BoujeeEnjinia1701/noisemap/cad/drawings/NSM-DWG-101.pdf

### BUILD PLAN SKETCH, PLAN NOT YET BUILT NoiseMap · github.com/BoujeeEnjinia1701/noisemap

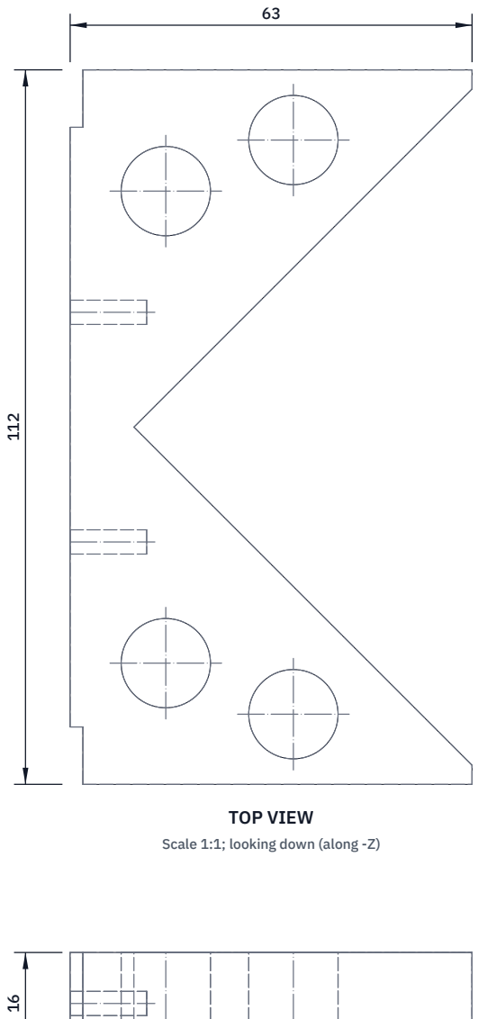
[picture p35: figure]
TOP VIEW; Scale 1:1; looking down (along -Z)

FRONT VIEW
Scale 1:1; looking at the front (along +Y)

RIGHT VIEW
Scale 1:1; looking at the right side (along -X)

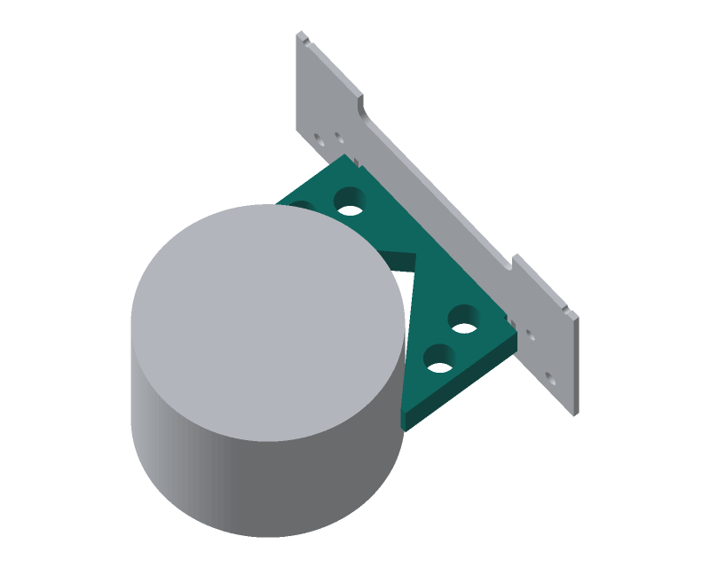
[picture p36: figure]

WHERE IT GOES
This part in colour, its neighbours in grey

HOW TO MAKE IT AND HOW IT FITS
Make two. Saw 112 mm off 70 x 16 mm bar; saw and file the width to 63 mm. The 112 x 16 face is the back; file it flat.
Scribe a 90 degree V on both 112 x 63 faces with a 45 degree square: 106 mm wide at the front face, point 10 mm from the back face.
Saw just inside both lines, file to the lines; keep the faces flat.
Rebate each back corner 9 mm wide and 2 mm deep, full height: the band passes under it. Round the front outer corners 3 mm. Drill four 14 mm lightening holes through: 15 mm from the back at 37 mm each side, and 35 mm from the back at 45 mm each side. Drill 3.3 mm, 14 deep, tap M4 12 deep in the back face at 18 mm each side of centre, half way up (8 mm).
Fit: two M4 countersunk screws from the box side of the FieldNode back plate. A 114 mm pole touches both V faces 40 mm off centre. Check: on a 114 mm tube the block must not rock.
REV | DESCRIPTION | DATE | BY
P1 | Making sketch for the prototype build plan | 2026-10-01 | AC
NOISEMAP | github.com/BoujeeEnjinia1701/noisemap

## NoiseMap street pole V-block (make 2): making sketch

DRAWING NO.
NSM-DWG-101

REV
P1

SHEET
1 of 1

SIZE

## ANSI B

SCALE
1:1

UNITS
mm
PROJECTION | DATE
2026-10-01

DRAWN
Amish Chadha

MATERIAL / NOTES
Aluminium flat bar 70 x 16 mm, 6082 or 6061 class
Licensed CERN-OHL-S-2.0 · Design Molecule Lab · designmolecule.com | Generated from cad/src; do not edit by hand
