BoujeeEnjinia1701/noisemap/cad/drawings/NSM-DWG-102.pdf

### BUILD PLAN SKETCH, PLAN NOT YET BUILT NoiseMap · github.com/BoujeeEnjinia1701/noisemap

FRONT VIEW
Scale 1:2; looking at the front (along +Y)

TOP VIEW
Scale 1:2; looking down (along -Z)

RIGHT VIEW
Scale 1:2; looking at the right side (along -X)

65

114 124

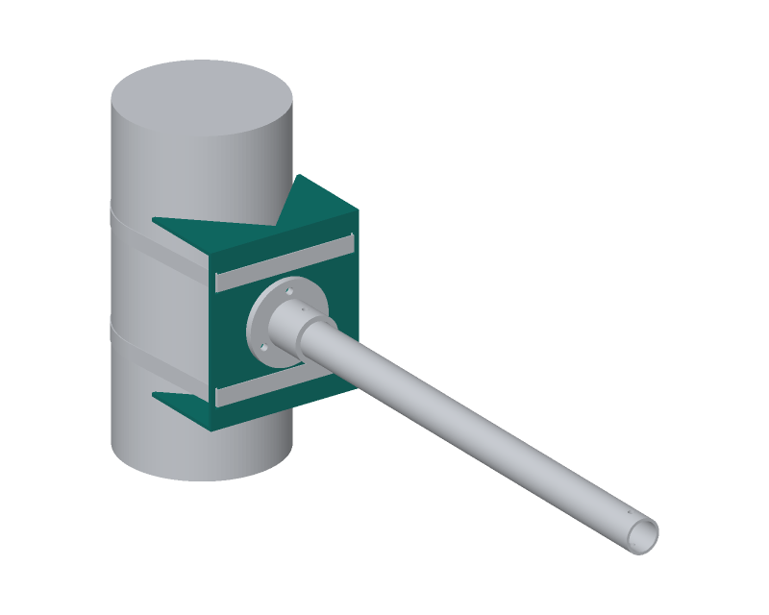
[picture p37: figure]

WHERE IT GOES
This part in colour, its neighbours in grey

HOW TO MAKE IT AND HOW IT FITS
A channel: web 114 wide x 124 tall, two flanges standing 65 out (outside sizes). Blank 114 wide; the bending shop sets its length. Cut a 90 degree V in each end of the blank (these become the flanges): 109 mm wide at the end, point 54.5 mm in from the end. Web: four band slots 3 x 15 at 52 mm each side of centre, centred 40 mm above and below the middle; chain drill 3 mm, file square. Web: three 5.5 mm holes on a 45 mm circle round the middle, one straight up, for the tube flange.
Bend both flanges 90 degrees the same way, inside radius about 3. Deburr and round the V edges so they cannot score the pole.
Fit: the pole bears on the four V edges; each band runs round
the pole, through two slots and across the outside of the web. Check: on a 114 mm tube all four V edges touch and it does not rock.
REV | DESCRIPTION | DATE | BY
P1 | Making sketch for the prototype build plan | 2026-10-01 | AC
NOISEMAP | github.com/BoujeeEnjinia1701/noisemap

## NoiseMap arm saddle: making sketch

DRAWING NO.
NSM-DWG-102

REV
P1

SHEET
1 of 1

SIZE

## ANSI B

SCALE
1:2

UNITS
mm
PROJECTION | DATE
2026-10-01

DRAWN
Amish Chadha

MATERIAL / NOTES
Aluminium sheet 2.5 mm, 5052-H32 (bends without cracking)
Licensed CERN-OHL-S-2.0 · Design Molecule Lab · designmolecule.com | Generated from cad/src; do not edit by hand
