BoujeeEnjinia1701/noisemap/cad/drawings/NSM-DWG-103.pdf

### BUILD PLAN SKETCH, PLAN NOT YET BUILT NoiseMap · github.com/BoujeeEnjinia1701/noisemap

FRONT VIEW
Scale 1:2; looking at the front (along +Y)

TOP VIEW
Scale 1:2; looking down (along -Z)

RIGHT VIEW
Scale 1:2; looking at the right side (along -X)

383

25 25

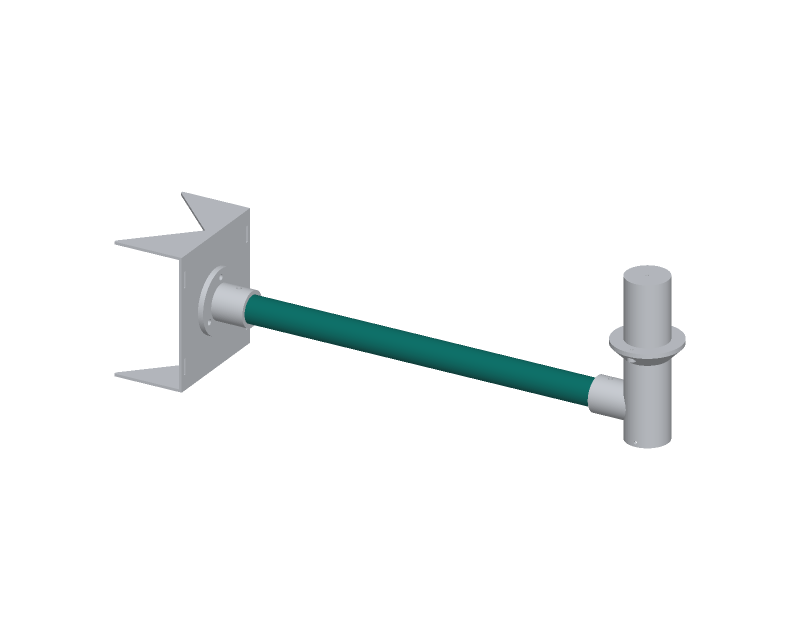
[picture p38: figure]

WHERE IT GOES
This part in colour, its neighbours in grey

HOW TO MAKE IT AND HOW IT FITS
Cut 383 mm of 25 x 2 mm tube; square and deburr both ends. Mark one end as the pole end.
Drill 4.6 mm straight through, top to bottom, 12.5 mm from the pole end (the flange cross bolt).
Drill 4.6 mm straight through, in the same plane, 12.5 mm from the far end (the head cross bolt).
Drill both holes on a drill press with the tube in a V-block so each hole passes through the centre line.
Fit: the pole end goes 25 mm into the tube flange's socket, the far end 25 mm into the head's socket; one bolt through each. Check: both holes line up when you sight along the tube.
REV | DESCRIPTION | DATE | BY
P1 | Making sketch for the prototype build plan | 2026-10-01 | AC
NOISEMAP | github.com/BoujeeEnjinia1701/noisemap

## NoiseMap arm tube: making sketch

DRAWING NO.
NSM-DWG-103

REV
P1

SHEET
1 of 1

SIZE

## ANSI B

SCALE
1:2

UNITS
mm
PROJECTION | DATE
2026-10-01

DRAWN
Amish Chadha

MATERIAL / NOTES
Aluminium round tube 25 x 2 mm, 6063
Licensed CERN-OHL-S-2.0 · Design Molecule Lab · designmolecule.com | Generated from cad/src; do not edit by hand
