BoujeeEnjinia1701/noisemap/cad/drawings/NSM-DWG-104.pdf

### BUILD PLAN SKETCH, PLAN NOT YET BUILT NoiseMap · github.com/BoujeeEnjinia1701/noisemap

FRONT VIEW
Scale 1:2; looking at the front (along +Y)

TOP VIEW
Scale 1:2; looking down (along -Z)

RIGHT VIEW
Scale 1:2; looking at the right side (along -X)

80

64 150

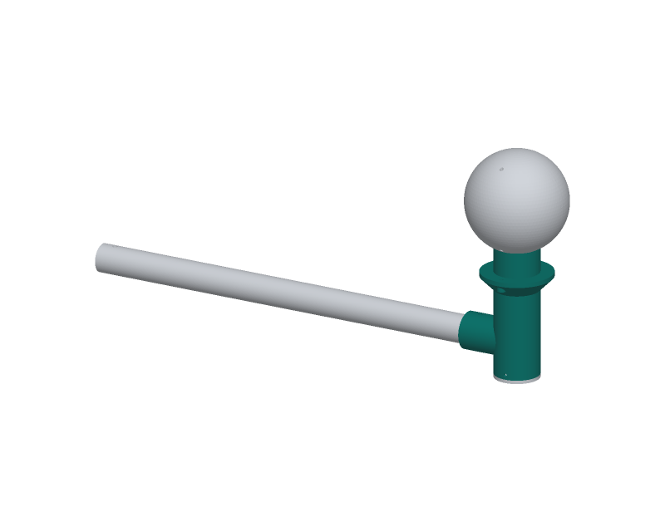
[picture p39: figure]

WHERE IT GOES
This part in colour, its neighbours in grey

HOW TO MAKE IT AND HOW IT FITS
Tube 40 OD x 3 wall x 150 tall, closed at the top by a 2 mm plate with a 3 mm acoustic port on the axis.
Drip skirt 64 OD, its top 58 below the port; 45 degree cone under it so it prints without support. Spike boss on it, 26 off the axis.
Arm socket 33 OD, bore 25.4, 25 deep, its axis 120 below the port; 4.4 mm cross hole 12.5 in from its open end, top to bottom. Inside: two card guides with 1.8 mm slots for the processor board; two 5 mm bosses under the top plate, 20 apart, for the mic board. Two 3.2 mm holes 4 above the open end for the cap screws.
Print standing on the top plate, supports under the arm socket only. Press an M3 heat-set insert into the spike boss.
Check: the port is clear; a 25 mm tube slides into the socket.
REV | DESCRIPTION | DATE | BY
P1 | Making sketch for the prototype build plan | 2026-10-01 | AC
NOISEMAP | github.com/BoujeeEnjinia1701/noisemap

## NoiseMap head housing: making sketch

DRAWING NO.
NSM-DWG-104

REV
P1

SHEET
1 of 1

SIZE

## ANSI B

SCALE
1:2

UNITS
mm
PROJECTION | DATE
2026-10-01

DRAWN
Amish Chadha

MATERIAL / NOTES
ASA, 3D printed, 4 walls, 40 % infill
Licensed CERN-OHL-S-2.0 · Design Molecule Lab · designmolecule.com | Generated from cad/src; do not edit by hand
