BoujeeEnjinia1701/noisemap/cad/drawings/NSM-DWG-105.pdf

### BUILD PLAN SKETCH, PLAN NOT YET BUILT NoiseMap · github.com/BoujeeEnjinia1701/noisemap

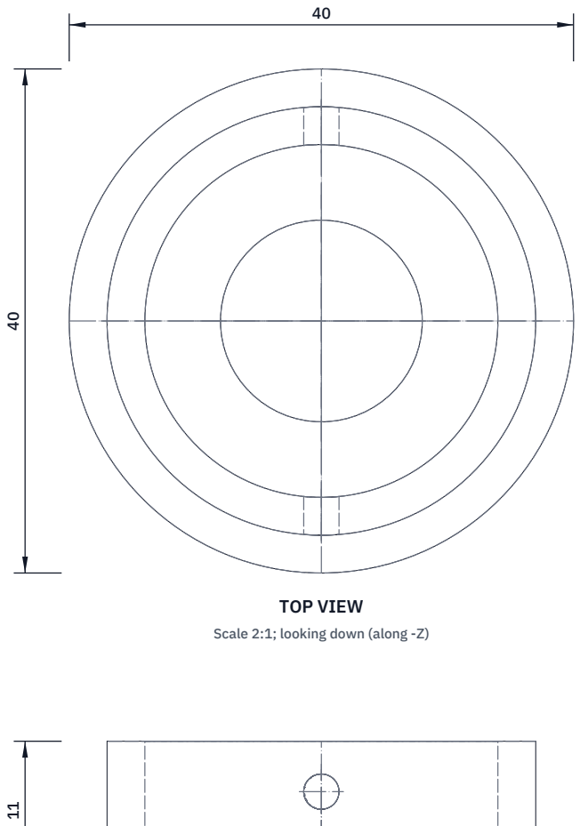
[picture p40: figure]
TOP VIEW; Scale 2:1; looking down (along -Z)

FRONT VIEW
Scale 2:1; looking at the front (along +Y)

RIGHT VIEW
Scale 2:1; looking at the right side (along -X)

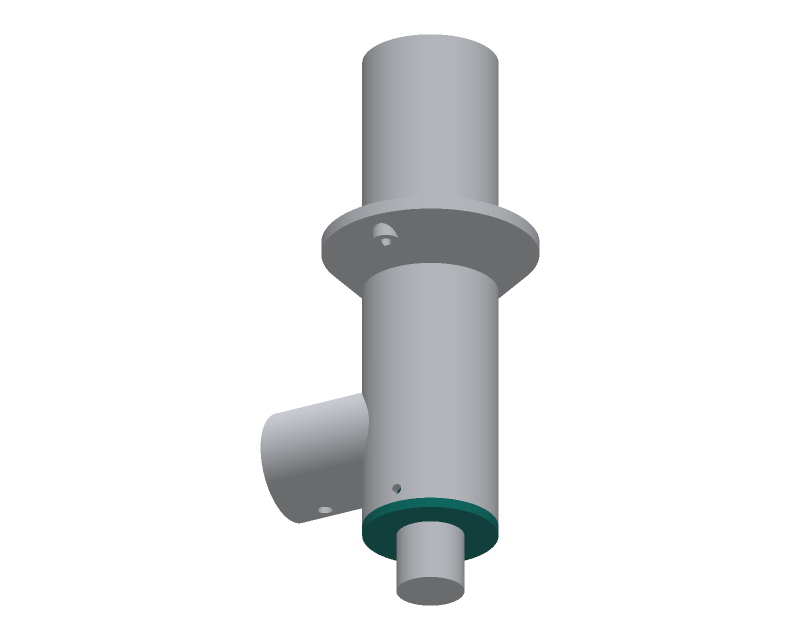
[picture p41: figure]

WHERE IT GOES
This part in colour, its neighbours in grey

HOW TO MAKE IT AND HOW IT FITS
Disc 40 OD x 3 thick with a ring standing 8 on it: 34 OD, 3 wall. 16 mm hole on the axis for the M16 cable gland.
Two 2.8 mm holes across the ring, 4 up from the disc, opposite each other, for the M3 screws (they self-tap into the ring). Print disc down; no supports.
Fit: the ring slides into the open end of the head until the disc meets the tube; two M3 x 6 screws through the head wall.
The gland goes through the 16 mm hole from below, nut inside. Check: the ring slides in by hand; the screw holes line up.
REV | DESCRIPTION | DATE | BY
P1 | Making sketch for the prototype build plan | 2026-10-01 | AC
NOISEMAP | github.com/BoujeeEnjinia1701/noisemap

## NoiseMap head bottom cap: making sketch

DRAWING NO.
NSM-DWG-105

REV
P1

SHEET
1 of 1

SIZE

## ANSI B

SCALE
2:1

UNITS
mm
PROJECTION | DATE
2026-10-01

DRAWN
Amish Chadha

MATERIAL / NOTES
ASA, 3D printed, solid
Licensed CERN-OHL-S-2.0 · Design Molecule Lab · designmolecule.com | Generated from cad/src; do not edit by hand
