BoujeeEnjinia1701/noisemap/cad/drawings/NSM-DWG-001.png

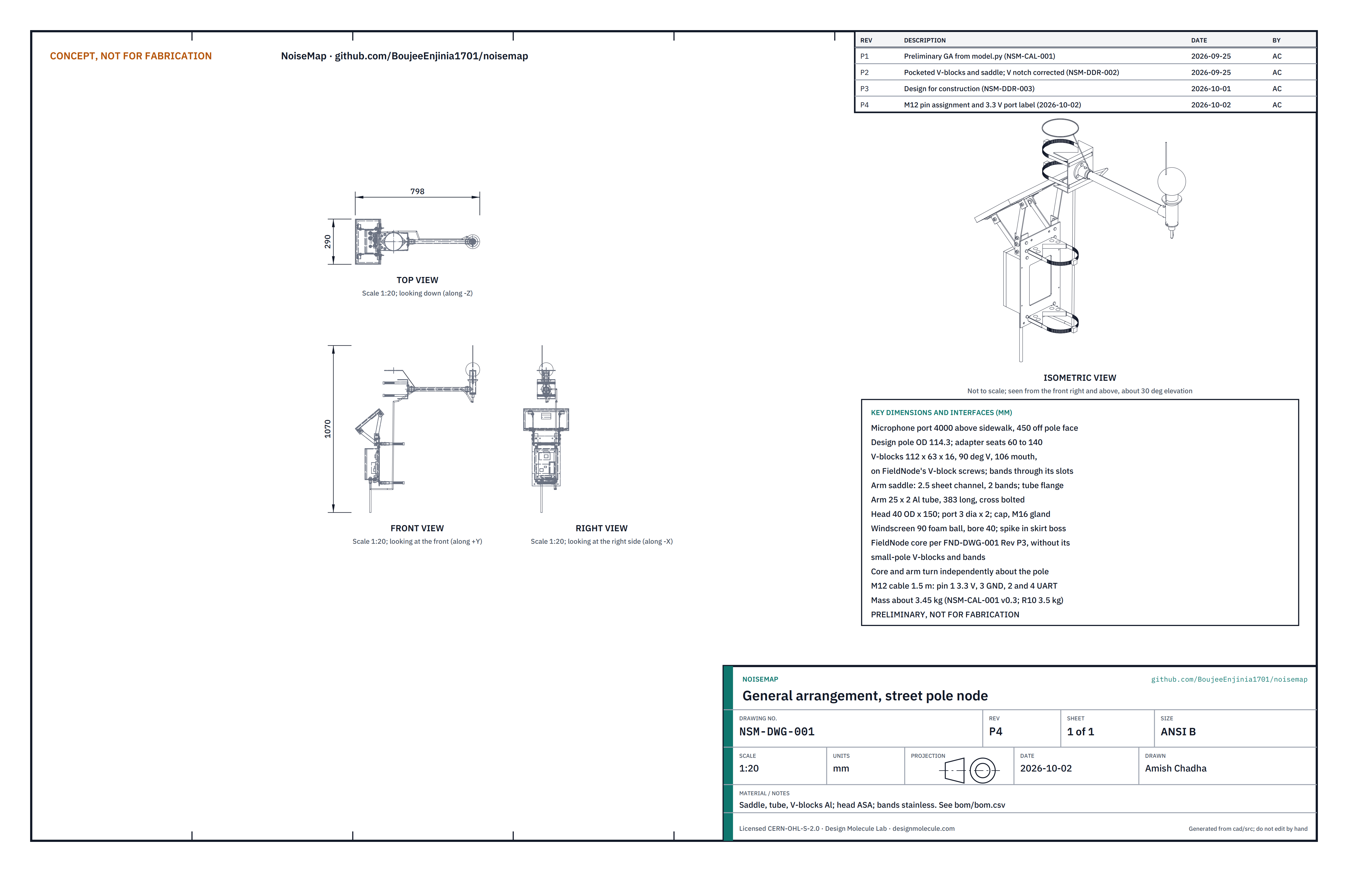
cad/drawings/NSM-DWG-001.png
