BoujeeEnjinia1701/noisemap/media/card.png

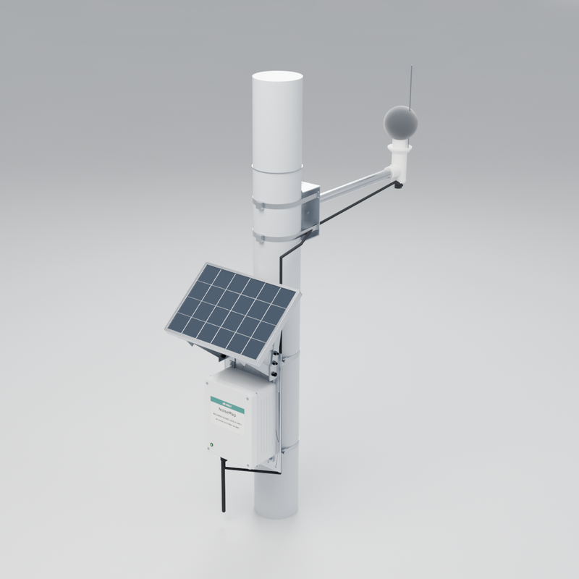
media/card.png
