BoujeeEnjinia1701/noisemap/media/render-detail.png

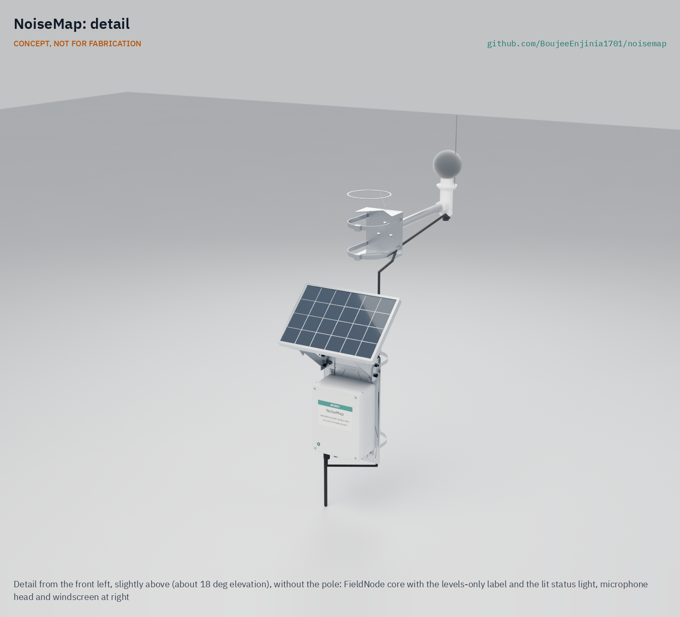
media/render-detail.png
