BoujeeEnjinia1701/noisemap/media/render-exploded.png

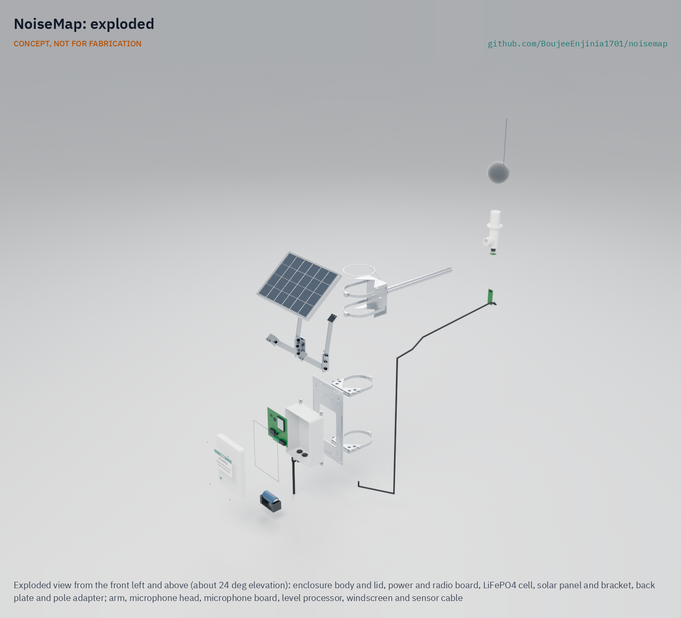
media/render-exploded.png
