BoujeeEnjinia1701/noisemap/media/social-preview.png

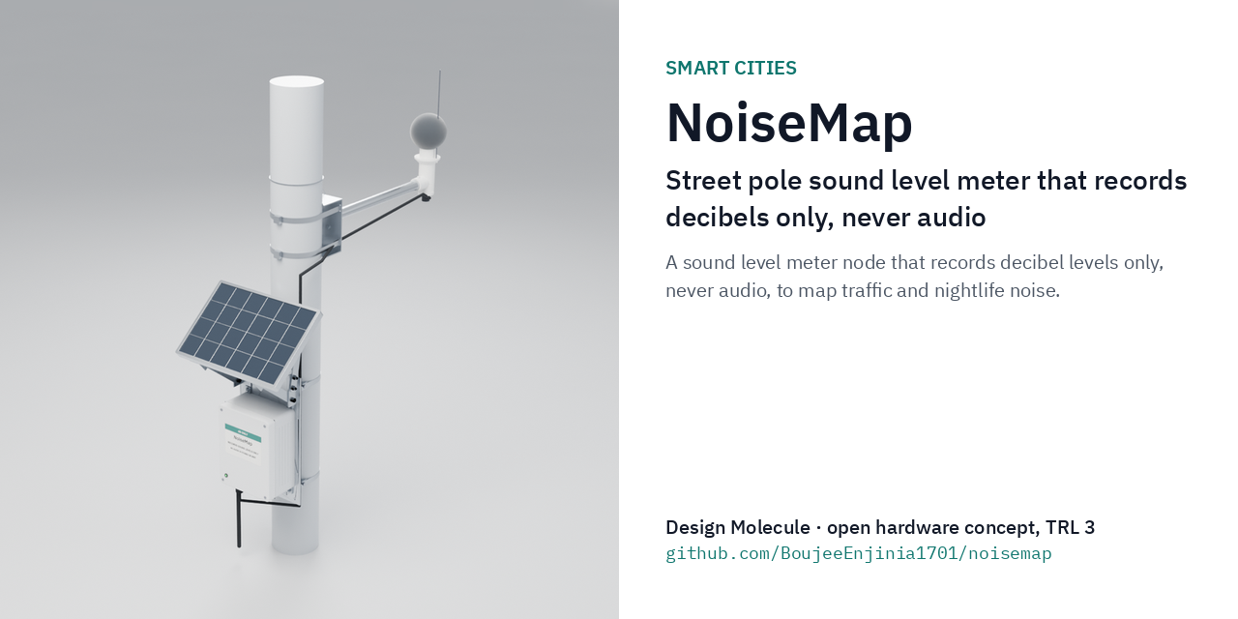
media/social-preview.png
