BoujeeEnjinia1701/noisemap/cad/drawings/NSM-DWG-106.pdf

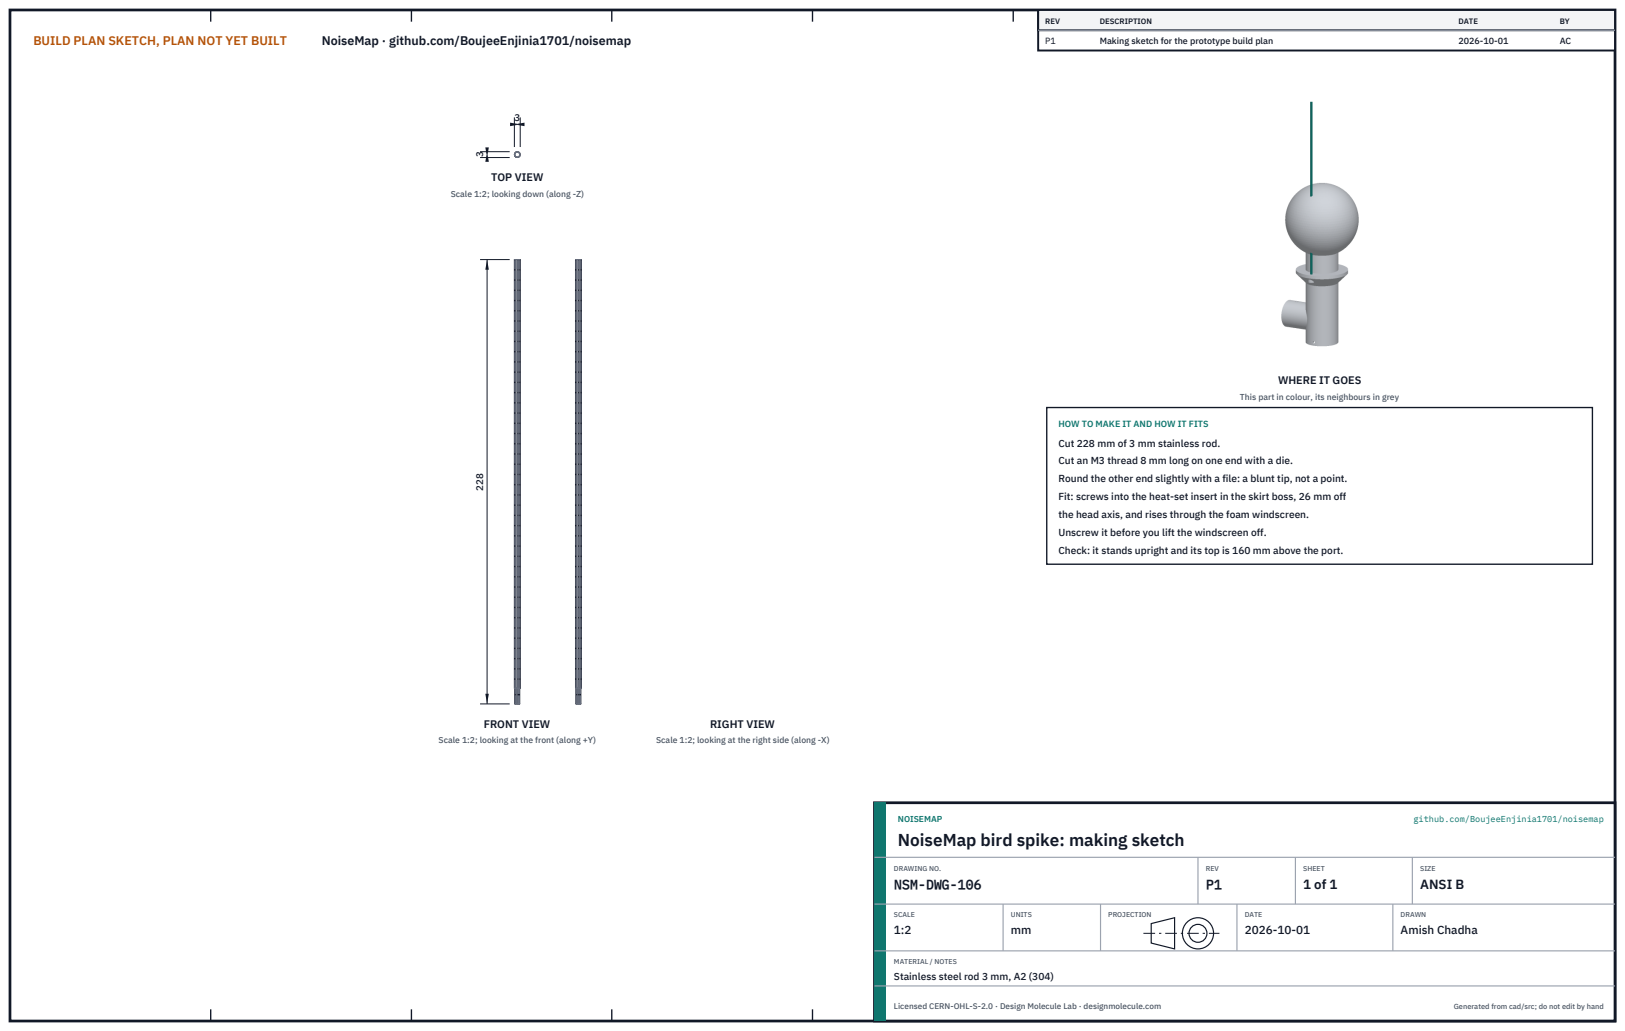
[picture p58: page 1]
BUILD PLAN SKETCH, PLAN NOT YET BUILT; NoiseMap · github.com/BoujeeEnjinia1701/noisemap; FRONT VIEW; TOP VIEW; RIGHT VIEW; REV; DESCRIPTION; DATE; Making sketch for the prototype build plan; NOISEMAP; github.com/BoujeeEnjinia1701/noisemap; DRAWING NO. NSM-DWG-106; REV P1; SHEET 1 of 1; SIZE ANSI B; SCALE 1:2; UNITS mm; PROJECTION; DRAWN Amish Chadha; Licensed CERN-OHL-S-2.0 · Design Molecule Lab · designmolecule.com; Generated from cad/src; do not edit by hand

Scale 1:2; looking down (along -Z)

WHERE IT GOES

This part in colour, its neighbours in grey

HOW TO MAKE IT AND HOW IT FITS
Cut 228 mm of 3 mm stainless rod.
Cut an M3 thread 8 mm long on one end with a die.
Round the other end slightly with a file: a blunt tip, not a point.
Fit: screws into the heat-set insert in the skirt boss, 26 mm off
the head axis, and rises through the foam windscreen.
Unscrew it before you lift the windscreen off.
Check: it stands upright and its top is 160 mm above the port.

Scale 1:2; looking at the front (along +Y)

Scale 1:2; looking at the right side (along -X)

NoiseMap bird spike: making sketch

MATERIAL / NOTES
Stainless steel rod 3 mm, A2 (304)
